wottle/lisa-mini/models/print-ready/Lisa_Mini_With_ESFloppy_Screen_And_Buttons_On_Front/Lisa_Mini_ESFloppy_Button_Inner_qty3.obj

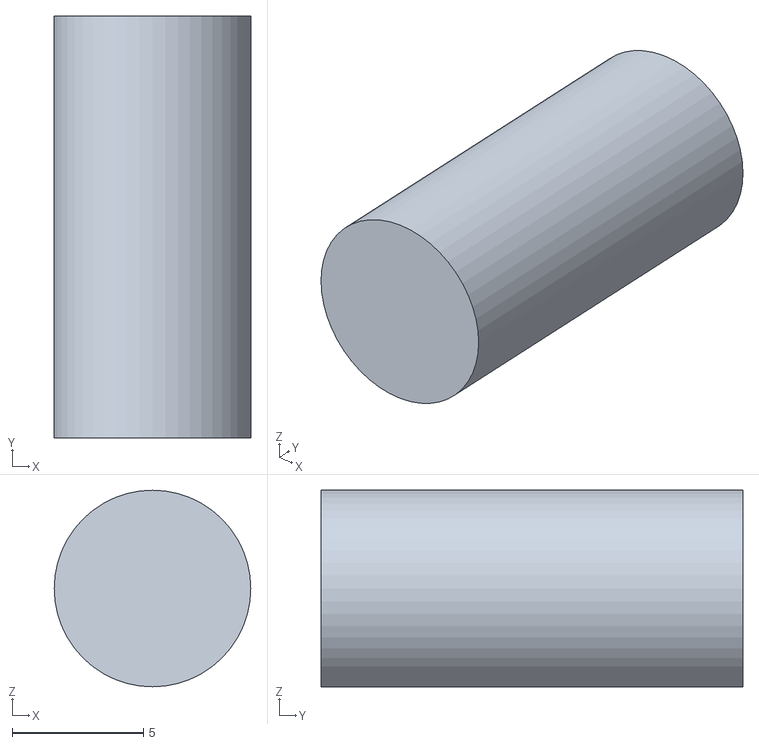
[picture p20: CAD file, 2026-10-08]
models/print-ready/Lisa_Mini_With_ESFloppy_Screen_And_Buttons_On_Front/Lisa_Mini_ESFloppy_Button_Inner_qty3.obj
7.50 x 16.1 x 7.50
