wottle/lisa-mini/models/print-ready/Lisa_Mini_With_ESFloppy_Screen_And_Buttons_On_Front/Lisa_Mini_Power-Button.stl

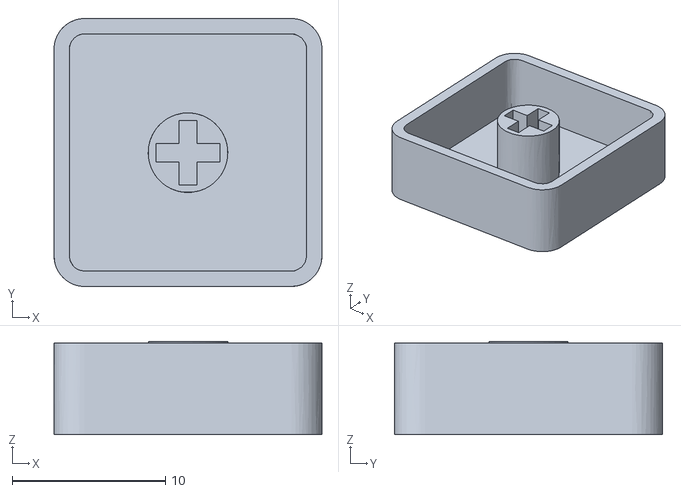
[picture p21: CAD file, 2026-10-08]
models/print-ready/Lisa_Mini_With_ESFloppy_Screen_And_Buttons_On_Front/Lisa_Mini_Power-Button.stl
17.5 x 17.5 x 6.10
